mattgp32/Low-Cost-Insulin-Pump-V2.1/src/ins_rate.c

/* This module written by Matt Payne as part of the Bluetooth insulin pump project.
   This module is used to store and control insulin delivery data
   Started on 20/3/2023
*/

#include "stdint.h"
#include "string.h"
#include "stdio.h"
#include "nvs_flash.h"
#include "esp_system.h"
#include "esp_log.h"
#include "freertos/FreeRTOS.h"
#include "freertos/task.h"
#include "freertos/event_groups.h"
#include "freertos/queue.h" 
#include "freertos/semphr.h"
#include "leds.h"
#include "time.h"
#include "sys/time.h"
#include "driver/gptimer.h"
#include "motor.h"
#include "driver/gpio.h"

#define STEPS_PER_UNIT 775 //(altered based on testing)
#define SECONDS_TO_MS 1000
#define THREE_MINUTES 180
#define SECONDS_IN_AN_HOUR 3600
#define MIN_DELIVERY_SIZE 25
#define MIN_DELIVERY_STEPS 18
#define MIN_BOLUS_DELIVERY_SIZE 50
#define MIN_BOLUS_DELIVERY_STEPS 36

uint8_t index_arr[2] = {0};
time_t esp_time;
time_t actual_time;
time_t unix_modifier = 0;
struct tm * timeinfo;

QueueHandle_t bolus_delivery_queue;

TickType_t frequency = 1000;
int basal_info_array[2];
extern int pot_read_global;
bool bolus_ready = false;
bool RW_flag = false;
extern bool disable_BT;


// Function to slice a string and find the index of two asterisks contained within it

bool check_bolus_cancelled() {
    int bolus_size = 0;
    nvs_handle_t bo_handle;
    bool cancelled = false;
    nvs_flash_init_partition("rate_storage");
    nvs_open_from_partition("rate_storage", "bolus_size", NVS_READWRITE, &bo_handle);   
    nvs_get_i32(bo_handle, "bolus_size", &bolus_size);


    if(bolus_size==0){
        cancelled = true;
    }

    return cancelled;
}
void slice_string(const char *data)
{
    uint8_t index = 0;
    memset(index_arr, 0, sizeof(index_arr));
    
    for(uint8_t i = 0; (i < strlen(data)); i++)
    {
        if(data[i] == 42)
        {
            index_arr[index] = i;
            index++;
        }
    }
}

void init_rate_storage_nvs_partition(void)
{
    
    //esp_err_t ret;
    nvs_flash_init_partition("rate_storage");
    // if (ret == ESP_OK)
    // {
    //     printf("Partition succesfully initialised\n");
    // }
}

void write_bolus_data(int delivery_amount)
{
    nvs_handle_t bo_handle;
    nvs_open_from_partition("rate_storage", "bolus_size", NVS_READWRITE, &bo_handle);
    delivery_amount = (delivery_amount / 25) * 25; //force answer to a multiple of 0.025U
    if (delivery_amount <= 0){
        led_double_flash();
    }
     nvs_set_i32(bo_handle, "bolus_size", delivery_amount);
     nvs_commit(bo_handle);
}

void write_basal_rate_data(int delivery_amount)
{
    nvs_handle_t br_handle;
    nvs_open_from_partition("rate_storage", "basal_rate", NVS_READWRITE, &br_handle);
    delivery_amount = (delivery_amount / 25) * 25; //force answer to a multiple of 0.025U
    if (delivery_amount <= 0){
        led_double_flash();
    }
    
    // switch (ret)
    // {
    // case ESP_OK:
    //     printf("Partition open successful\n");
    //     break;
    // case ESP_FAIL:
    //     printf("Internal Error\n");
    //     break;
    // case ESP_ERR_NVS_NOT_INITIALIZED:
    //     printf("Partition not initialised\n");
    //     break;
    // case ESP_ERR_NVS_INVALID_NAME:
    //     printf("Name doesnt meet constraints\n");
    //     break;
    // default:
    //     printf("Some other error, work it out yourself!\n");
    //     break;
    // }

    nvs_set_i32(br_handle, "basal_rate", delivery_amount);

    // switch (ret)
    // {
    // case ESP_OK:
    //     printf("Data written\n");
    //     break;
    // case ESP_FAIL:
    //     printf("Internal Error\n");
    //     break;
    // case ESP_ERR_NVS_INVALID_HANDLE:
    //     printf("Handle has been closed or == NULL\n");
    //     break;
    // case ESP_ERR_NVS_READ_ONLY:
    //     printf("Didnt open as read write\n");
    //     break;
    // case ESP_ERR_NVS_NOT_ENOUGH_SPACE:
    //     printf("Not enough memory buddy\n");
    //     break;
    // default:
    //     printf("Some other error, work it out yourself!\n");
    //     break;
    // }

    nvs_commit(br_handle);
    // switch (ret)
    // {
    // case ESP_OK:
    //     printf("Data commited\n");
    //     break;
    // case ESP_ERR_NVS_INVALID_HANDLE:
    //     printf("Handle has been closed or == NULL\n");
    //     break;
    // default:
    //     printf("Some other error, work it out yourself!\n");
    //     break;
    // }
}

void write_rewind_data(int delivery_amount)
{
    nvs_handle_t br_handle;
    nvs_open_from_partition("rate_storage", "rewi", NVS_READWRITE, &br_handle);
    delivery_amount = (delivery_amount / 25) * 25; //force answer to a multiple of 0.025U
    if (delivery_amount <= 0){
        led_double_flash();
    }

    nvs_set_i32(br_handle, "basal_rate", delivery_amount);
    nvs_commit(br_handle);
   
}

int set_delivery_frequency(void)
{
    int basal_rate = 0;
    nvs_handle_t br_handle;

    nvs_flash_init_partition("rate_storage");
    nvs_open_from_partition("rate_storage", "basal_rate", NVS_READONLY, &br_handle);
    nvs_get_i32(br_handle, "basal_rate", &basal_rate);

    int dels_per_hour = basal_rate / MIN_DELIVERY_SIZE;
    int dels_freq;

    if (dels_per_hour <=0) {
        dels_freq = 0;
    } else if (dels_per_hour < 20){
        dels_freq = SECONDS_IN_AN_HOUR/dels_per_hour; //seconds between doses = dels_freq
    }
    else {
        dels_freq = THREE_MINUTES;
    }
    basal_info_array[0] = dels_per_hour;
    basal_info_array[1] = basal_rate;

    return dels_freq;
}

int set_delivery_frequency_test(int freq)
{
    return freq;
}

void read_and_store_data(const char *data)
{
    char data_type[3];
    strncpy(data_type, data, 2);
    data_type[2] = '\0';
    printf("The data type here is %s\n", data_type);
    
    if(strcmp(data_type, "TI") == 0){
        //printf("This is a time type\n");
        slice_string(data);
        //printf("Index values are at %d, %d\n", index_arr[0], index_arr[1]);
        char unix_time[index_arr[1]-index_arr[0]];
        strncpy(&unix_time[0], &data[index_arr[0]+1], index_arr[1]-index_arr[0]-1);
        unix_time[10] = '\0';
         unix_modifier = atoi(unix_time);
        //printf("UNIX time = %lld\n", unix_modifier);

    } else if (strcmp(data_type, "BA") == 0) {
        float basal_rate = 0;
        int basal_rate_i = 0;
        //printf("This is of basal insulin delivery type\n");
        slice_string(data);
        //printf("Index values are at %d, %d\n", index_arr[0], index_arr[1]);
        char basal_delivery[index_arr[1]-index_arr[0]];
        basal_delivery[index_arr[1]-index_arr[0]-1] = '\0';
        strncpy(basal_delivery, &data[index_arr[0]+1] , (index_arr[1] - index_arr[0])-1);
        basal_rate = atof(basal_delivery);
        basal_rate_i = basal_rate*1000;
        //printf("Current basal rate is %d\n", basal_rate_i);
        init_rate_storage_nvs_partition();
        write_basal_rate_data(basal_rate_i);

    } else if (strcmp(data_type, "BO") == 0) {
        float bolus_size = 0;
        int bolus_size_i = 0;
        //printf("This is of bolus insulin delivery type %s\n", data);
        slice_string(data);
        //printf("Index values are at %d, %d\n", index_arr[0], index_arr[1]);
        char bolus_delivery[index_arr[1]-index_arr[0]];
        bolus_delivery[index_arr[1]-index_arr[0]-1] = '\0';
        strncpy(bolus_delivery, &data[index_arr[0]+1] , (index_arr[1] - index_arr[0])-1);
        bolus_size = atof(bolus_delivery);
        bolus_size_i = bolus_size*1000;
        printf("Entered bolus_size is %d\n", bolus_size_i);
        init_rate_storage_nvs_partition();
        write_bolus_data(bolus_size_i);
        bolus_ready = true;
    } else if (strcmp(data_type, "RE") == 0) {
        RW_flag=true;
    } else if (strcmp(data_type, "PR") == 0) {
        float prime_size = 0;
        slice_string(data);
        char prime_delivery[index_arr[1]-index_arr[0]];
        prime_delivery[index_arr[1]-index_arr[0]-1] = '\0';
        strncpy(prime_delivery, &data[index_arr[0]+1] , (index_arr[1] - index_arr[0])-1);
        prime_size = atof(prime_delivery);
        printf("Entered prime amount is %d\n", (int)prime_size);

        for(int i = 0; i < (int)prime_size; i++){
            turn_x_steps(false, STEPS_PER_UNIT);
            vTaskDelay(pdMS_TO_TICKS(100));
        }

    } else {
         printf("You have entered an invalid type\n");
    }
}

//Just used for checking if nvs and BT was working, not used in final version
void retreive_data(void* arg)
{
    for(;;)
    {
    int basal_rate = 0;
    int bolus_size = 0;
    
    setenv("TZ", "UTC-12", 1);
    tzset();
    actual_time = time(&esp_time) + unix_modifier;
    timeinfo = localtime(&actual_time);
    
    printf ("Current local time and date: %s", asctime(timeinfo));

    nvs_handle_t br_handle;
    nvs_handle_t bo_handle;
    nvs_flash_init_partition("rate_storage");
    nvs_open_from_partition("rate_storage", "basal_rate", NVS_READONLY, &br_handle);
    nvs_open_from_partition("rate_storage", "bolus_size", NVS_READONLY, &bo_handle);
    nvs_get_i32(br_handle, "basal_rate", &basal_rate);
    nvs_get_i32(bo_handle, "bolus_size", &bolus_size);
    printf("Current basal rate is %d\n", basal_rate);
    printf("Current bolus amount is %d\n", bolus_size);
    vTaskDelay(pdMS_TO_TICKS(10000));
    }
}

void give_insulin(void* arg)
{
    for(;;)
    {
        frequency = set_delivery_frequency() * SECONDS_TO_MS;
        // frequency = set_delivery_frequency_test(500) * SECONDS_TO_MS;
        led_double_flash();

        if (frequency <= 0) {
            //puts("basal rate is 0");
            frequency = pdMS_TO_TICKS(THREE_MINUTES*SECONDS_TO_MS);
        } else {
        //puts("Entered motor control block\n");
        turn_x_steps(false, (int)(STEPS_PER_UNIT*basal_info_array[1])/(basal_info_array[0]*1000));
        // turn_x_steps(true, (int)(STEPS_PER_UNIT));
        }
    vTaskDelay(pdMS_TO_TICKS(frequency));
    //puts("I am working");
    }
}

void bolus_delivery(void* arg)
{
    for(;;)
    {
        nvs_handle_t bo_handle;
        int bolus_size = 0;

        if(bolus_ready == true)
        {
            nvs_flash_init_partition("rate_storage");
            nvs_open_from_partition("rate_storage", "bolus_size", NVS_READWRITE, &bo_handle);   
            nvs_get_i32(bo_handle, "bolus_size", &bolus_size);
                if((bolus_size/MIN_DELIVERY_SIZE) == 0){
                    puts("ReQueSteD bOLuS iS ToO SMalL!!!");
                    led_double_flash();
                } else {
                    int n_steps = bolus_size/MIN_BOLUS_DELIVERY_SIZE;
                    printf("Delivering %d doses of 0.05U\n", n_steps);
                    for(int i = 0; i < n_steps; i++){
                        if(!check_bolus_cancelled()){
                        turn_x_steps(false, MIN_BOLUS_DELIVERY_STEPS);
                        vTaskDelay(pdMS_TO_TICKS(1200));
                        } else {
                            puts("Bolus Cancelled");
                            break;
                        }
                    }

                    if((bolus_size % MIN_BOLUS_DELIVERY_SIZE) == MIN_DELIVERY_SIZE) {
                        turn_x_steps(false, MIN_DELIVERY_STEPS);
                        puts("Delivering 1 dose of 0.025U");
                    }

                    
                    puts("Bolus delivery complete");
                    //disable_BT = true;
            
            }
        }
        nvs_set_i32(bo_handle, "bolus_size", 0);
        nvs_commit(bo_handle);
        bolus_ready = false;
       
        vTaskDelay(pdMS_TO_TICKS(1000));
    } 
}

void rewind_plunge(void* arg)
{
    for(;;){
        if(RW_flag == true) {
            turn_x_steps(true, STEPS_PER_UNIT*2);
        }

        if(pot_read_global <=0){
            RW_flag = false;
        }
        vTaskDelay(pdMS_TO_TICKS(200));
    }
    
}
