mattgp32/Low-Cost-Insulin-Pump-V2.1/src/adc.c

/* This module written by Matt Payne as part of the Bluetooth insulin pump project.
   This module is designed to control the adc to take a reading of the battery level and determine if the device has a low battery.
   Started on 9/3/2023
*/
#include "freertos/FreeRTOS.h"
#include "freertos/task.h"
#include "freertos/queue.h" 
#include "freertos/timers.h"
#include "freertos/event_groups.h"
#include "freertos/semphr.h"

#include "esp_adc/adc_oneshot.h"
#include "adc.h"


QueueHandle_t battLevelQueue;
QueueHandle_t potReadQueue;
int pot_read_global;

//setup and initialise an adc instance

void get_batt_level(void* arg)
{
    for(;;)
    {
    int adc_raw_value = 0;
    int *pBatt_level;

    battLevelQueue = xQueueCreate(3, sizeof(int));

    if (battLevelQueue==0)
    {
        //printf("Uh oh, the battery level queue craetion failed!");
    }

    // Initialise ADC1 Channel 7
    adc_oneshot_unit_handle_t batt_read_adc_handle;
    
    adc_oneshot_unit_init_cfg_t batt_read_adc_config = { .unit_id = ADC_UNIT_1,
                                                         .ulp_mode = ADC_ULP_MODE_DISABLE,};

    ESP_ERROR_CHECK(adc_oneshot_new_unit(&batt_read_adc_config, &batt_read_adc_handle));

    adc_oneshot_chan_cfg_t config = {.bitwidth = ADC_BITWIDTH_DEFAULT,
                                     .atten = ADC_ATTEN_DB_11,};

    adc_oneshot_config_channel(batt_read_adc_handle, ADC_CHANNEL_7, &config);

    adc_oneshot_read(batt_read_adc_handle, ADC_CHANNEL_7, &adc_raw_value);

    // Close adc instance and free up memory/peripherals
    ESP_ERROR_CHECK(adc_oneshot_del_unit(batt_read_adc_handle));

    int batt_level = ((adc_raw_value * 3100)/4095) + 300;
    pBatt_level = &batt_level;

    xQueueSend(battLevelQueue, pBatt_level, 0);
    vTaskDelay(pdMS_TO_TICKS(10000));
    }

}

void print_batt_level(void* arg)
{
    int* pBattLevel;
    int battlevel;
    pBattLevel = &battlevel;

    xQueueReceive(battLevelQueue, pBattLevel, 10);

    printf("Current battery level is %d mV", battlevel); // This print was just to check the function works during development and it does. Hence I have commentented it out. 
    // If you want to put it back in make sure you increase the freertos stack size of this function or it will crash 

    vTaskDelay(10000/portTICK_PERIOD_MS);
}

void read_pot(void* arg)
{
    for(;;)
    {


    int adc_raw_value = 0;
    int i = 0;
    int potsumtot = 0;
    
    gpio_set_direction(GPIO_NUM_2, GPIO_MODE_INPUT);
    gpio_pullup_dis(GPIO_NUM_2);
    gpio_pulldown_dis(GPIO_NUM_2);
    gpio_set_direction(GPIO_NUM_37, GPIO_MODE_OUTPUT);
    gpio_set_level(GPIO_NUM_37, true);
    vTaskDelay(pdMS_TO_TICKS(1000));
   

    while(i<10)
    {

    potReadQueue = xQueueCreate(3, sizeof(int));

    // Initialise ADC1 Channel 1
    adc_oneshot_unit_handle_t pot_read_adc_handle;
    
    adc_oneshot_unit_init_cfg_t pot_read_adc_config = { .unit_id = ADC_UNIT_1,
                                                         .ulp_mode = ADC_ULP_MODE_DISABLE,};

    ESP_ERROR_CHECK(adc_oneshot_new_unit(&pot_read_adc_config, &pot_read_adc_handle));

    adc_oneshot_chan_cfg_t config = {.bitwidth = ADC_BITWIDTH_DEFAULT,
                                     .atten = ADC_ATTEN_DB_11,};

    adc_oneshot_config_channel(pot_read_adc_handle, ADC_CHANNEL_1, &config);

    adc_oneshot_read(pot_read_adc_handle, ADC_CHANNEL_1, &adc_raw_value);

    // Close adc instance and free up memory/peripherals
    ESP_ERROR_CHECK(adc_oneshot_del_unit(pot_read_adc_handle));

    int potRead = adc_raw_value;
    
    i++;
    potsumtot += potRead;


    }
    pot_read_global = potsumtot/10;
    printf("Pot read = %d\n", pot_read_global);
    gpio_set_level(GPIO_NUM_37, false);
    vTaskDelay(pdMS_TO_TICKS(10000));
    }
}
